zhangzq71/STEPFOC-stepper-controller/STEPFOC firmware/src/hw_init.cpp

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
/* Includes ------------------------------------------------------------------*/

#include "hw_init.h"

// TODO HAL sensor init
/// @brief Init all digital input pins
/// @param  
void Init_Digital_Inputs(void)
{


	pinMode(ADDITIONAL1, INPUT_PULLUP); //INPUT_PULLUP
	pinMode(ADDITIONAL2, INPUT_PULLUP); //INPUT_PULLUP

	//attachInterrupt(digitalPinToInterrupt(ADDITIONAL1),ADDITIONAL1_INTERRUPT,CHANGE);
	//attachInterrupt(digitalPinToInterrupt(ADDITIONAL2),ADDITIONAL2_INTERRUPT,CHANGE);


}

/// @brief  ADDITIONAL pin falling interrupt
void ADDITIONAL1_INTERRUPT(){

	controller.additional1_var = digitalReadFast(ADDITIONAL1);
}

/// @brief  ADDITIONAL pin falling interrupt
void ADDITIONAL2_INTERRUPT(){

	controller.additional2_var = digitalReadFast(ADDITIONAL2);
}

/// @brief Init all digital output pins
void Init_Digital_Outputs(void)
{

	pinMode(LED, OUTPUT);

}

/// @brief System clock config
void SystemClock_Config(void)
{

	RCC_OscInitTypeDef RCC_OscInitStruct;
	RCC_ClkInitTypeDef RCC_ClkInitStruct;

	/**Initializes the CPU, AHB and APB busses clocks
	 */
	RCC_OscInitStruct.OscillatorType = RCC_OSCILLATORTYPE_HSE;
	RCC_OscInitStruct.HSEState = RCC_HSE_ON;
	RCC_OscInitStruct.PLL.PLLState = RCC_PLL_NONE;
	if (HAL_RCC_OscConfig(&RCC_OscInitStruct) != HAL_OK)
	{
		_Error_Handler(__FILE__, __LINE__);
	}

	/**Initializes the CPU, AHB and APB busses clocks
	 */
	RCC_ClkInitStruct.ClockType = RCC_CLOCKTYPE_HCLK | RCC_CLOCKTYPE_SYSCLK | RCC_CLOCKTYPE_PCLK1 | RCC_CLOCKTYPE_PCLK2;
	RCC_ClkInitStruct.SYSCLKSource = RCC_SYSCLKSOURCE_HSE;
	RCC_ClkInitStruct.AHBCLKDivider = RCC_SYSCLK_DIV1;
	RCC_ClkInitStruct.APB1CLKDivider = RCC_HCLK_DIV2;
	RCC_ClkInitStruct.APB2CLKDivider = RCC_HCLK_DIV1;

	if (HAL_RCC_ClockConfig(&RCC_ClkInitStruct, FLASH_LATENCY_2) != HAL_OK)
	{
		_Error_Handler(__FILE__, __LINE__);
	}

	HAL_RCC_MCOConfig(RCC_MCO, RCC_MCO1SOURCE_HSE, RCC_MCODIV_1);

	/**Configure the Systick interrupt time
	 */
	HAL_SYSTICK_Config(HAL_RCC_GetHCLKFreq() / 1000);

	/**Configure the Systick
	 */
	HAL_SYSTICK_CLKSourceConfig(SYSTICK_CLKSOURCE_HCLK);

	/* SysTick_IRQn interrupt configuration */
	HAL_NVIC_SetPriority(SysTick_IRQn, 0, 0);
}

/// @brief  Init system clock
/// @param multiplier clock multiplier
/// Default clock multiplier is 16 for 128Mhz clock speed
void TM_SystemClock_Config(int multiplier)
{

	RCC_OscInitTypeDef RCC_OscInitStruct;
	RCC_ClkInitTypeDef RCC_ClkInitStruct;

	// revert to HSE source
	RCC_ClkInitStruct.ClockType = RCC_CLOCKTYPE_HCLK | RCC_CLOCKTYPE_SYSCLK | RCC_CLOCKTYPE_PCLK1 | RCC_CLOCKTYPE_PCLK2;
	RCC_ClkInitStruct.SYSCLKSource = RCC_SYSCLKSOURCE_HSE; // <- HSE
	RCC_ClkInitStruct.AHBCLKDivider = RCC_SYSCLK_DIV1;
	RCC_ClkInitStruct.APB1CLKDivider = RCC_HCLK_DIV2;
	RCC_ClkInitStruct.APB2CLKDivider = RCC_HCLK_DIV1;

	if (HAL_RCC_ClockConfig(&RCC_ClkInitStruct, FLASH_LATENCY_0) != HAL_OK)
	{
		_Error_Handler(__FILE__, __LINE__);
	}

	// Setup PLL with new multiplier
	RCC_OscInitStruct.OscillatorType = RCC_OSCILLATORTYPE_HSE;
	RCC_OscInitStruct.HSEState = RCC_HSE_ON;
	RCC_OscInitStruct.HSEPredivValue = RCC_HSE_PREDIV_DIV1;
	RCC_OscInitStruct.HSIState = RCC_HSI_ON;
	RCC_OscInitStruct.PLL.PLLState = RCC_PLL_ON;
	RCC_OscInitStruct.PLL.PLLSource = RCC_PLLSOURCE_HSE;

	// set clock multiplier
	if (multiplier == 9)
	{
		RCC_OscInitStruct.PLL.PLLMUL = RCC_PLL_MUL9;
	}
	else if (multiplier == 10)
	{
		RCC_OscInitStruct.PLL.PLLMUL = RCC_PLL_MUL10;
	}
	else if (multiplier == 11)
	{
		RCC_OscInitStruct.PLL.PLLMUL = RCC_PLL_MUL11;
	}
	else if (multiplier == 12)
	{
		RCC_OscInitStruct.PLL.PLLMUL = RCC_PLL_MUL12;
	}
	else if (multiplier == 13)
	{
		RCC_OscInitStruct.PLL.PLLMUL = RCC_PLL_MUL13;
	}
	else if (multiplier == 14)
	{
		RCC_OscInitStruct.PLL.PLLMUL = RCC_PLL_MUL14;
	}
	else if (multiplier == 15)
	{
		RCC_OscInitStruct.PLL.PLLMUL = RCC_PLL_MUL15;
	}
	else if (multiplier == 16)
	{
		RCC_OscInitStruct.PLL.PLLMUL = RCC_PLL_MUL16;
	}
	else
	{ // if wrong number use stock speed
		RCC_OscInitStruct.PLL.PLLMUL = RCC_PLL_MUL9;
	}

	if (HAL_RCC_OscConfig(&RCC_OscInitStruct) != HAL_OK)
	{
		_Error_Handler(__FILE__, __LINE__);
	}

	// Go back to PLL source
	RCC_ClkInitStruct.ClockType = RCC_CLOCKTYPE_HCLK | RCC_CLOCKTYPE_SYSCLK | RCC_CLOCKTYPE_PCLK1 | RCC_CLOCKTYPE_PCLK2;
	RCC_ClkInitStruct.SYSCLKSource = RCC_SYSCLKSOURCE_PLLCLK; // <- PLL welcome back
	RCC_ClkInitStruct.AHBCLKDivider = RCC_SYSCLK_DIV1;
	RCC_ClkInitStruct.APB1CLKDivider = RCC_HCLK_DIV2;
	RCC_ClkInitStruct.APB2CLKDivider = RCC_HCLK_DIV1;

	if (HAL_RCC_ClockConfig(&RCC_ClkInitStruct, FLASH_LATENCY_2) != HAL_OK)
	{
		_Error_Handler(__FILE__, __LINE__);
	}

	/**Configure the Systick interrupt time
	 */
	HAL_SYSTICK_Config(HAL_RCC_GetHCLKFreq() / 1000);

	/**Configure the Systick
	 */
	HAL_SYSTICK_CLKSourceConfig(SYSTICK_CLKSOURCE_HCLK);

	/* SysTick_IRQn interrupt configuration */
	HAL_NVIC_SetPriority(SysTick_IRQn, 0, 0);
}
